Code99it/4F5LCD/displaypreviews/preview91D4.png

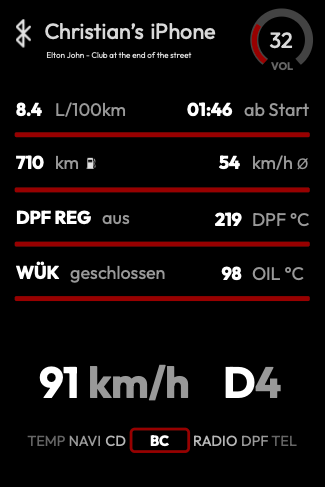
displaypreviews/preview91D4.png
