Code99it/4F5LCD/displaypreviews/preview.png

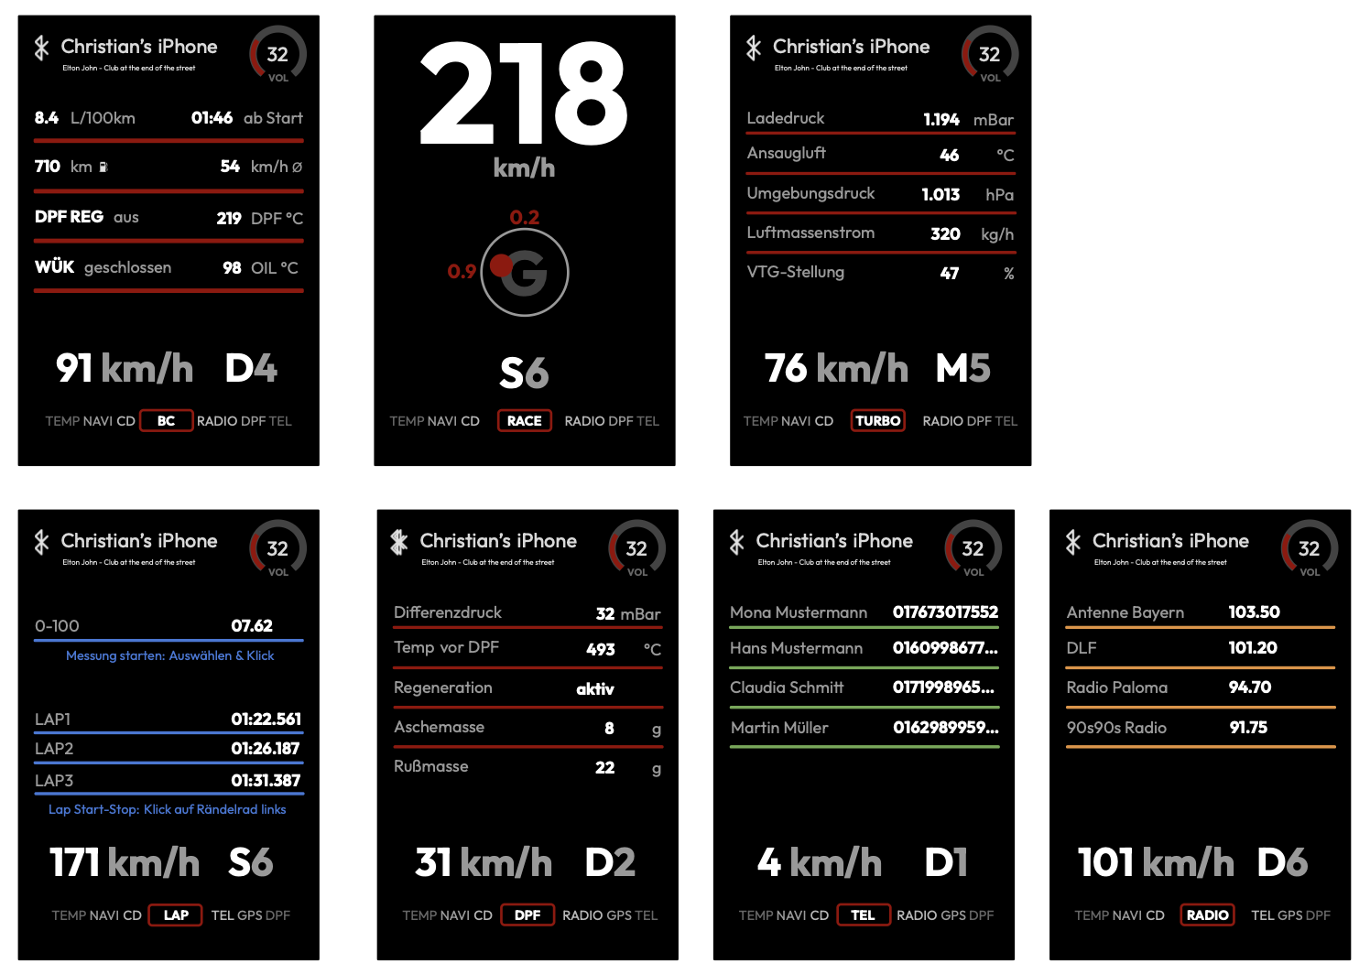
displaypreviews/preview.png
