Code99it/4F5LCD/ESP32-project/fonts/how-to-cut-a-letter.png

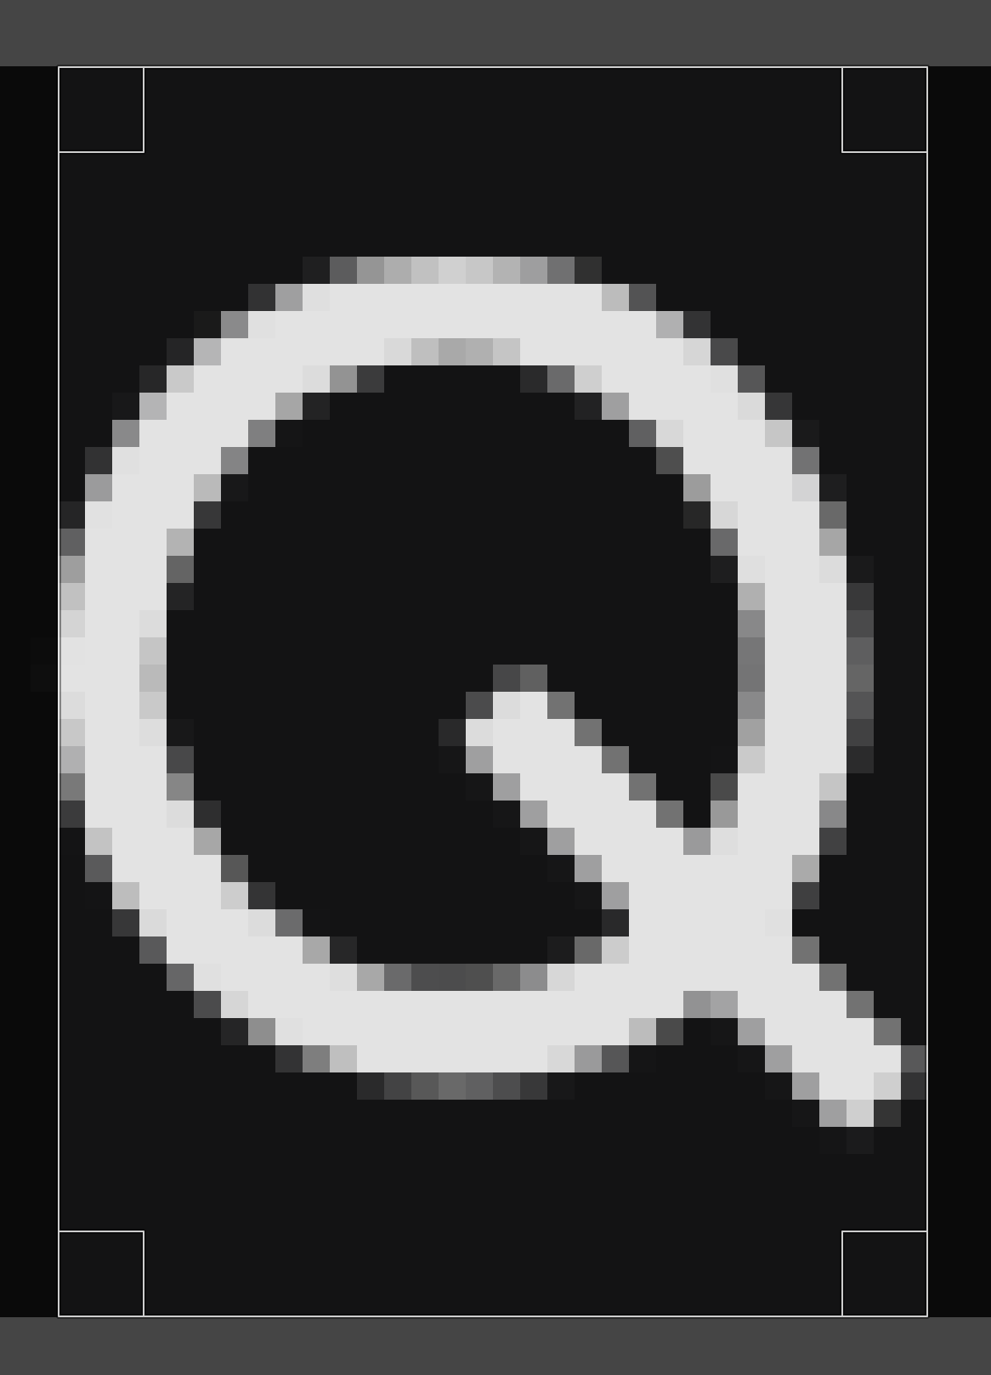
ESP32-project/fonts/how-to-cut-a-letter.png
