Code99it/4F5LCD/Solution 1 - 3D printed mounting frame for the LCD/PXL_20250601_192038704.jpg

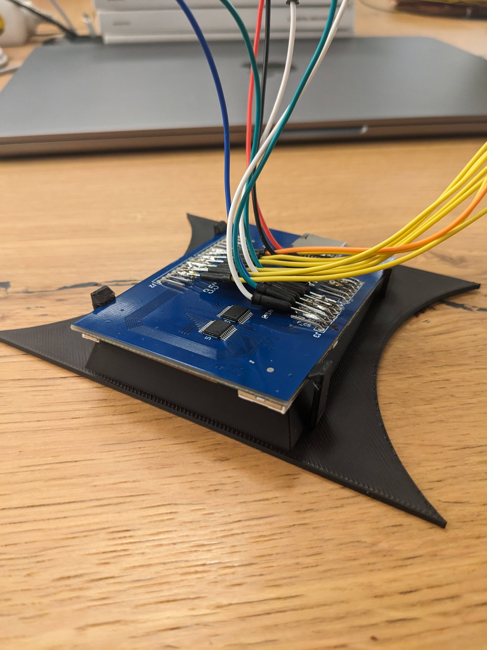
Solution 1 - 3D printed mounting frame for the LCD/PXL_20250601_192038704.jpg
