Code99it/4F5LCD/Solution 2 - Disassembling the speedometer and fitting a 3.5 inch display/PXL_20250607_091444971.jpg

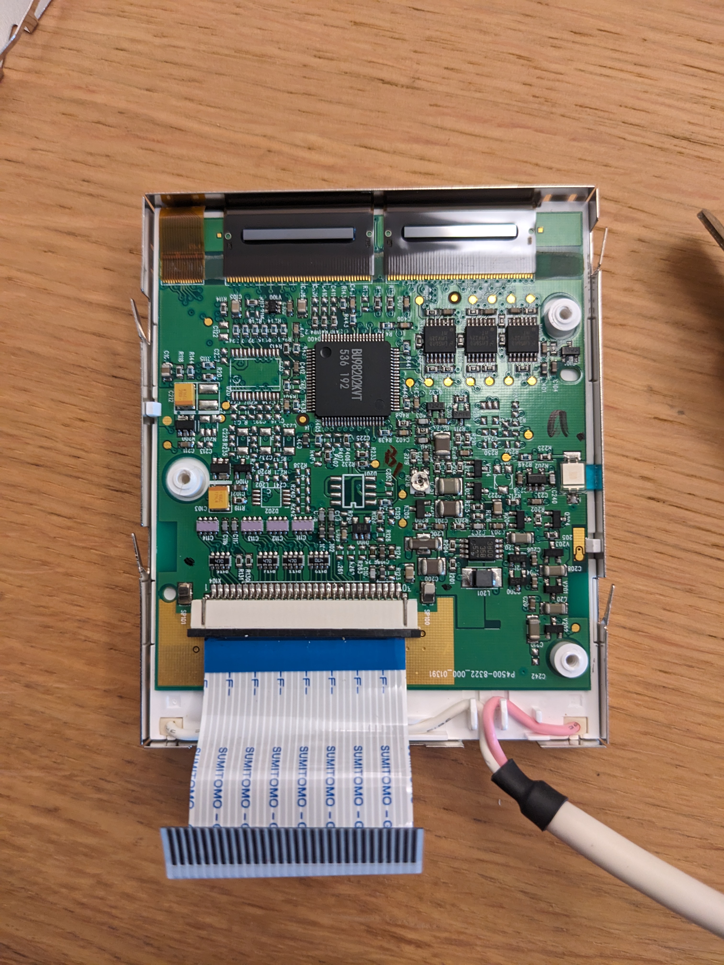
Solution 2 - Disassembling the speedometer and fitting a 3.5 inch display/PXL_20250607_091444971.jpg
