Code99it/4F5LCD/PCB printed circuit board/KiCad/100powersupply.kicad_sch

## KiCad design PCB printed circuit board/KiCad/100powersupply.kicad_sch (2025-06-01)

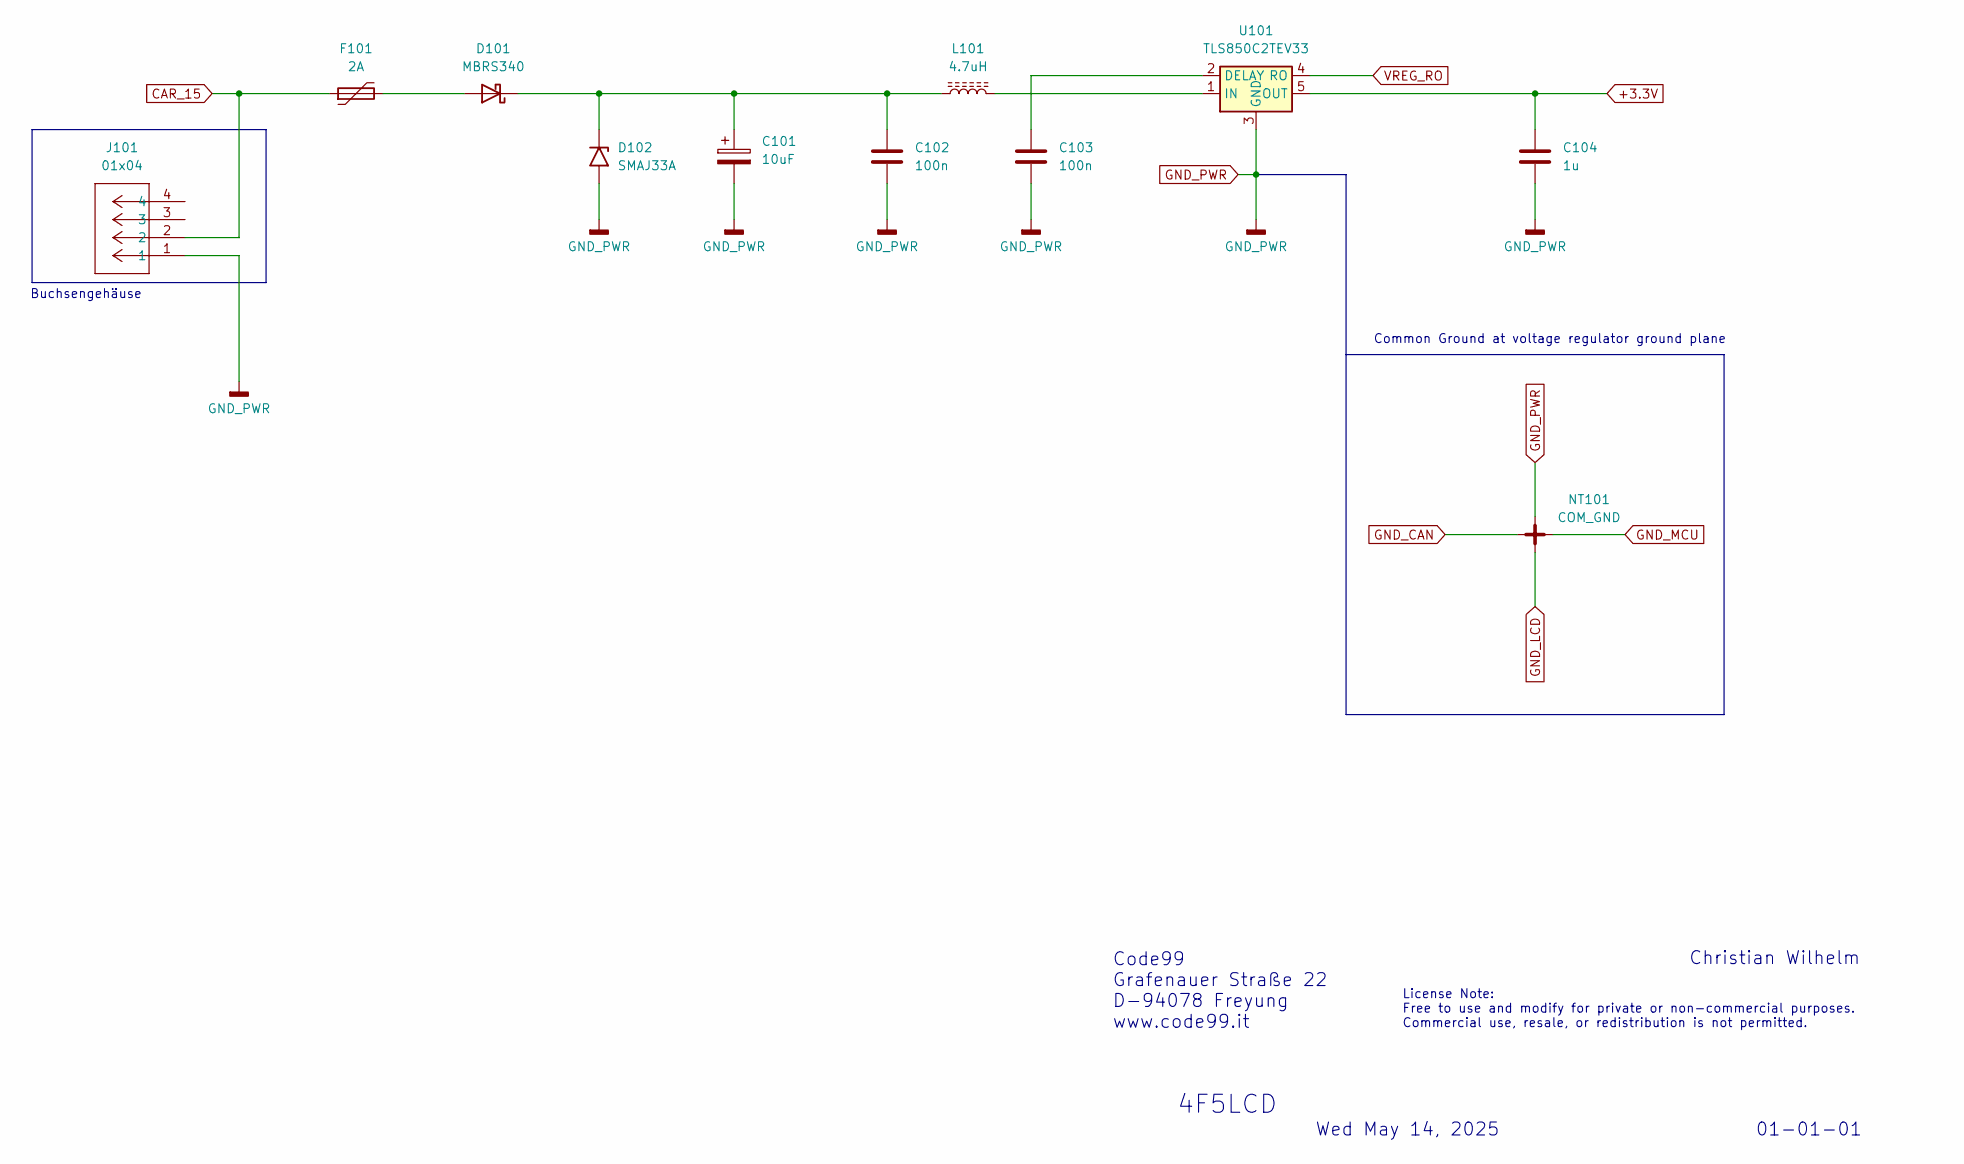
[picture p49: schematic 100powersupply.kicad_sch]

Parts:
C101: 10uF; CP_Elec_5x5.9; Farnell 2346378
C102, C103: 100n; C_1206_3216Metric_Pad1.33x1.80mm_HandSolder; Farnell 2495443
C104: 1u; C_1206_3216Metric_Pad1.33x1.80mm_HandSolder; Farnell 2357339
D101: MBRS340; D_SMC; Farnell 2824888
D102: SMAJ33A; D_SMA; Farnell 4065376
F101: 2A; Fuse_Bourns_MF-SM_7.98x5.44mm; Farnell 3605928
J101: 01x04; TE_MATE-N-LOK_1-770968-x_2x02_P4.14mm_Horizontal; Farnell 3394275
L101: 4.7uH; L_Radial_D7.5mm_P5.00mm_Fastron_07P
NT101: COM_GND
U101: TLS850C2TEV33; TO-252-4; Farnell 3680235

Connections:
+3.3V: C104.1, U101.5 (OUT)
CAR_15: F101.1, J101.2
GND_CAN: NT101.1
GND_LCD: NT101.4
GND_MCU: NT101.2
GND_PWR: C101.2, C102.2, C103.2, C104.2, D102.2 (A2), J101.1, NT101.3, U101.3 (GND)
unnamed: C101.1, C102.1, D101.1 (K), D102.1 (A1), L101.1
unnamed: C103.1, U101.2 (DELAY)
unnamed: D101.2 (A), F101.2
unnamed: L101.2, U101.1 (IN)
VREG_RO: U101.4 (RO)

Notes on the sheet:
Wed May 14, 2025
Code99 Grafenauer Straße 22 D-94078 Freyung www.code99.it
License Note: Free to use and modify for private or non-commercial purposes. Commercial use, resale, or redistribution is not permitted.
4F5LCD
01-01-01
Buchsengehäuse
Common Ground at voltage regulator ground plane
Christian Wilhelm
