Code99it/4F5LCD/PCB printed circuit board/KiCad/200mcuesp32.kicad_sch

## KiCad design PCB printed circuit board/KiCad/200mcuesp32.kicad_sch (2025-06-01)

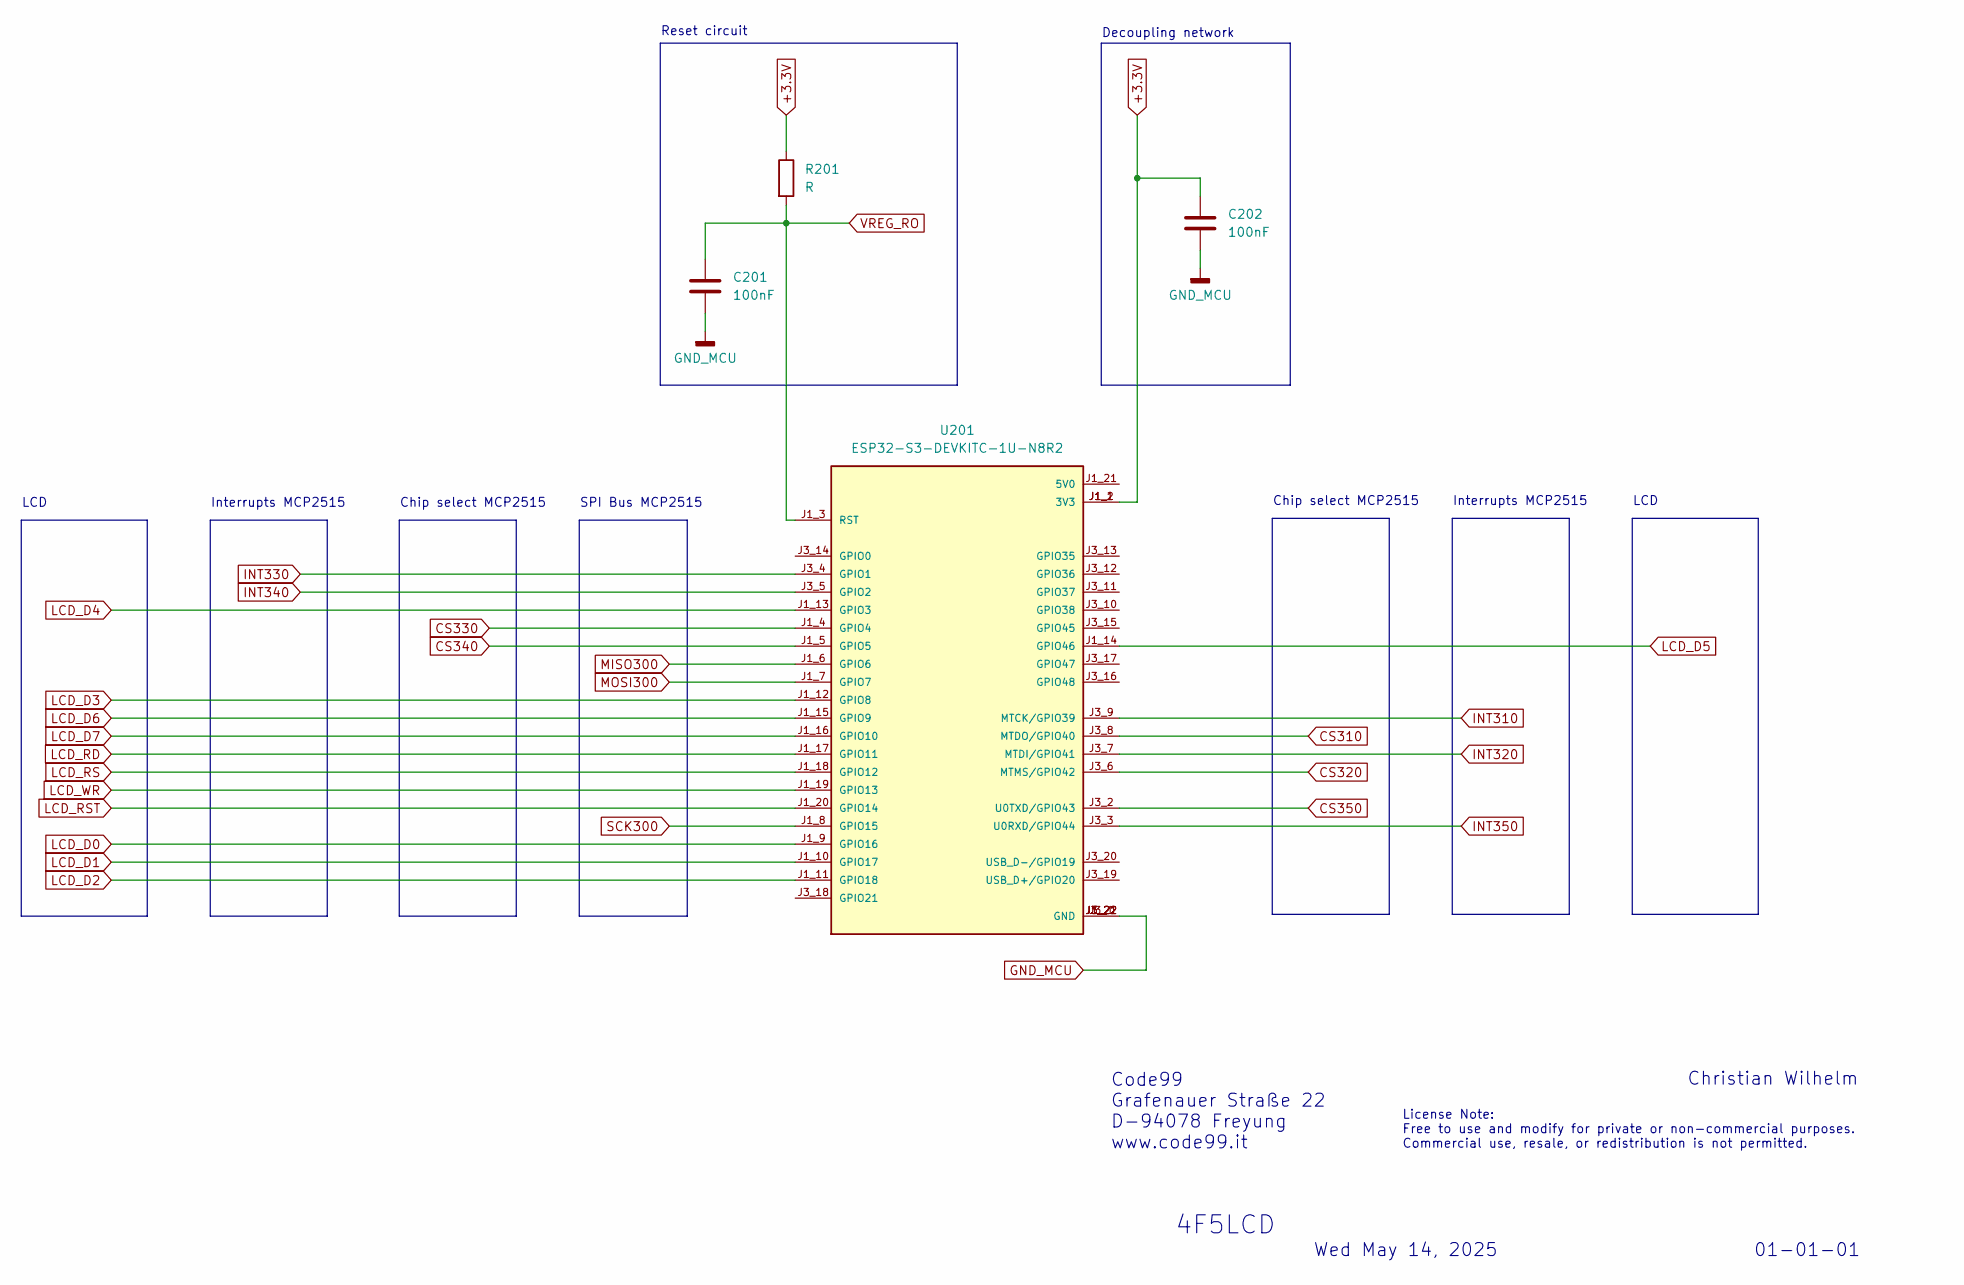
[picture p50: schematic 200mcuesp32.kicad_sch]

Parts:
C201: 100nF; Farnell 2495443
C202: 100nF; C_1206_3216Metric_Pad1.33x1.80mm_HandSolder; Farnell 2495443
R201: R; Farnell 1469856
U201: ESP32-S3-DEVKITC-1U-N8R2; XCVR_ESP32-S3-DEVKITC-1U-N8R2; PARTREV 5.3

Connections:
+3.3V: C202.1, R201.1, U201.J1_1 (3V3), U201.J1_2 (3V3)
CS310: U201.J3_8 (MTDO/GPIO40)
CS320: U201.J3_6 (MTMS/GPIO42)
CS330: U201.J1_4 (GPIO4)
CS340: U201.J1_5 (GPIO5)
CS350: U201.J3_2 (U0TXD/GPIO43)
GND_MCU: C201.2, C202.2, U201.J1_22 (GND), U201.J3_1 (GND), U201.J3_21 (GND), U201.J3_22 (GND)
INT310: U201.J3_9 (MTCK/GPIO39)
INT320: U201.J3_7 (MTDI/GPIO41)
INT330: U201.J3_4 (GPIO1)
INT340: U201.J3_5 (GPIO2)
INT350: U201.J3_3 (U0RXD/GPIO44)
LCD_D0: U201.J1_9 (GPIO16)
LCD_D1: U201.J1_10 (GPIO17)
LCD_D2: U201.J1_11 (GPIO18)
LCD_D3: U201.J1_12 (GPIO8)
LCD_D4: U201.J1_13 (GPIO3)
LCD_D5: U201.J1_14 (GPIO46)
LCD_D6: U201.J1_15 (GPIO9)
LCD_D7: U201.J1_16 (GPIO10)
LCD_RD: U201.J1_17 (GPIO11)
LCD_RS: U201.J1_18 (GPIO12)
LCD_RST: U201.J1_20 (GPIO14)
LCD_WR: U201.J1_19 (GPIO13)
MISO300: U201.J1_6 (GPIO6)
MOSI300: U201.J1_7 (GPIO7)
SCK300: U201.J1_8 (GPIO15)
VREG_RO: C201.1, R201.2, U201.J1_3 (RST)

Notes on the sheet:
License Note: Free to use and modify for private or non-commercial purposes. Commercial use, resale, or redistribution is not permitted.
LCD
01-01-01
Reset circuit
Chip select MCP2515
Interrupts MCP2515
Code99 Grafenauer Straße 22 D-94078 Freyung www.code99.it
Decoupling network
4F5LCD
SPI Bus MCP2515
Christian Wilhelm
Wed May 14, 2025
