Code99it/4F5LCD/PCB printed circuit board/KiCad/310connector.kicad_sch

## KiCad design PCB printed circuit board/KiCad/310connector.kicad_sch (2025-06-01)

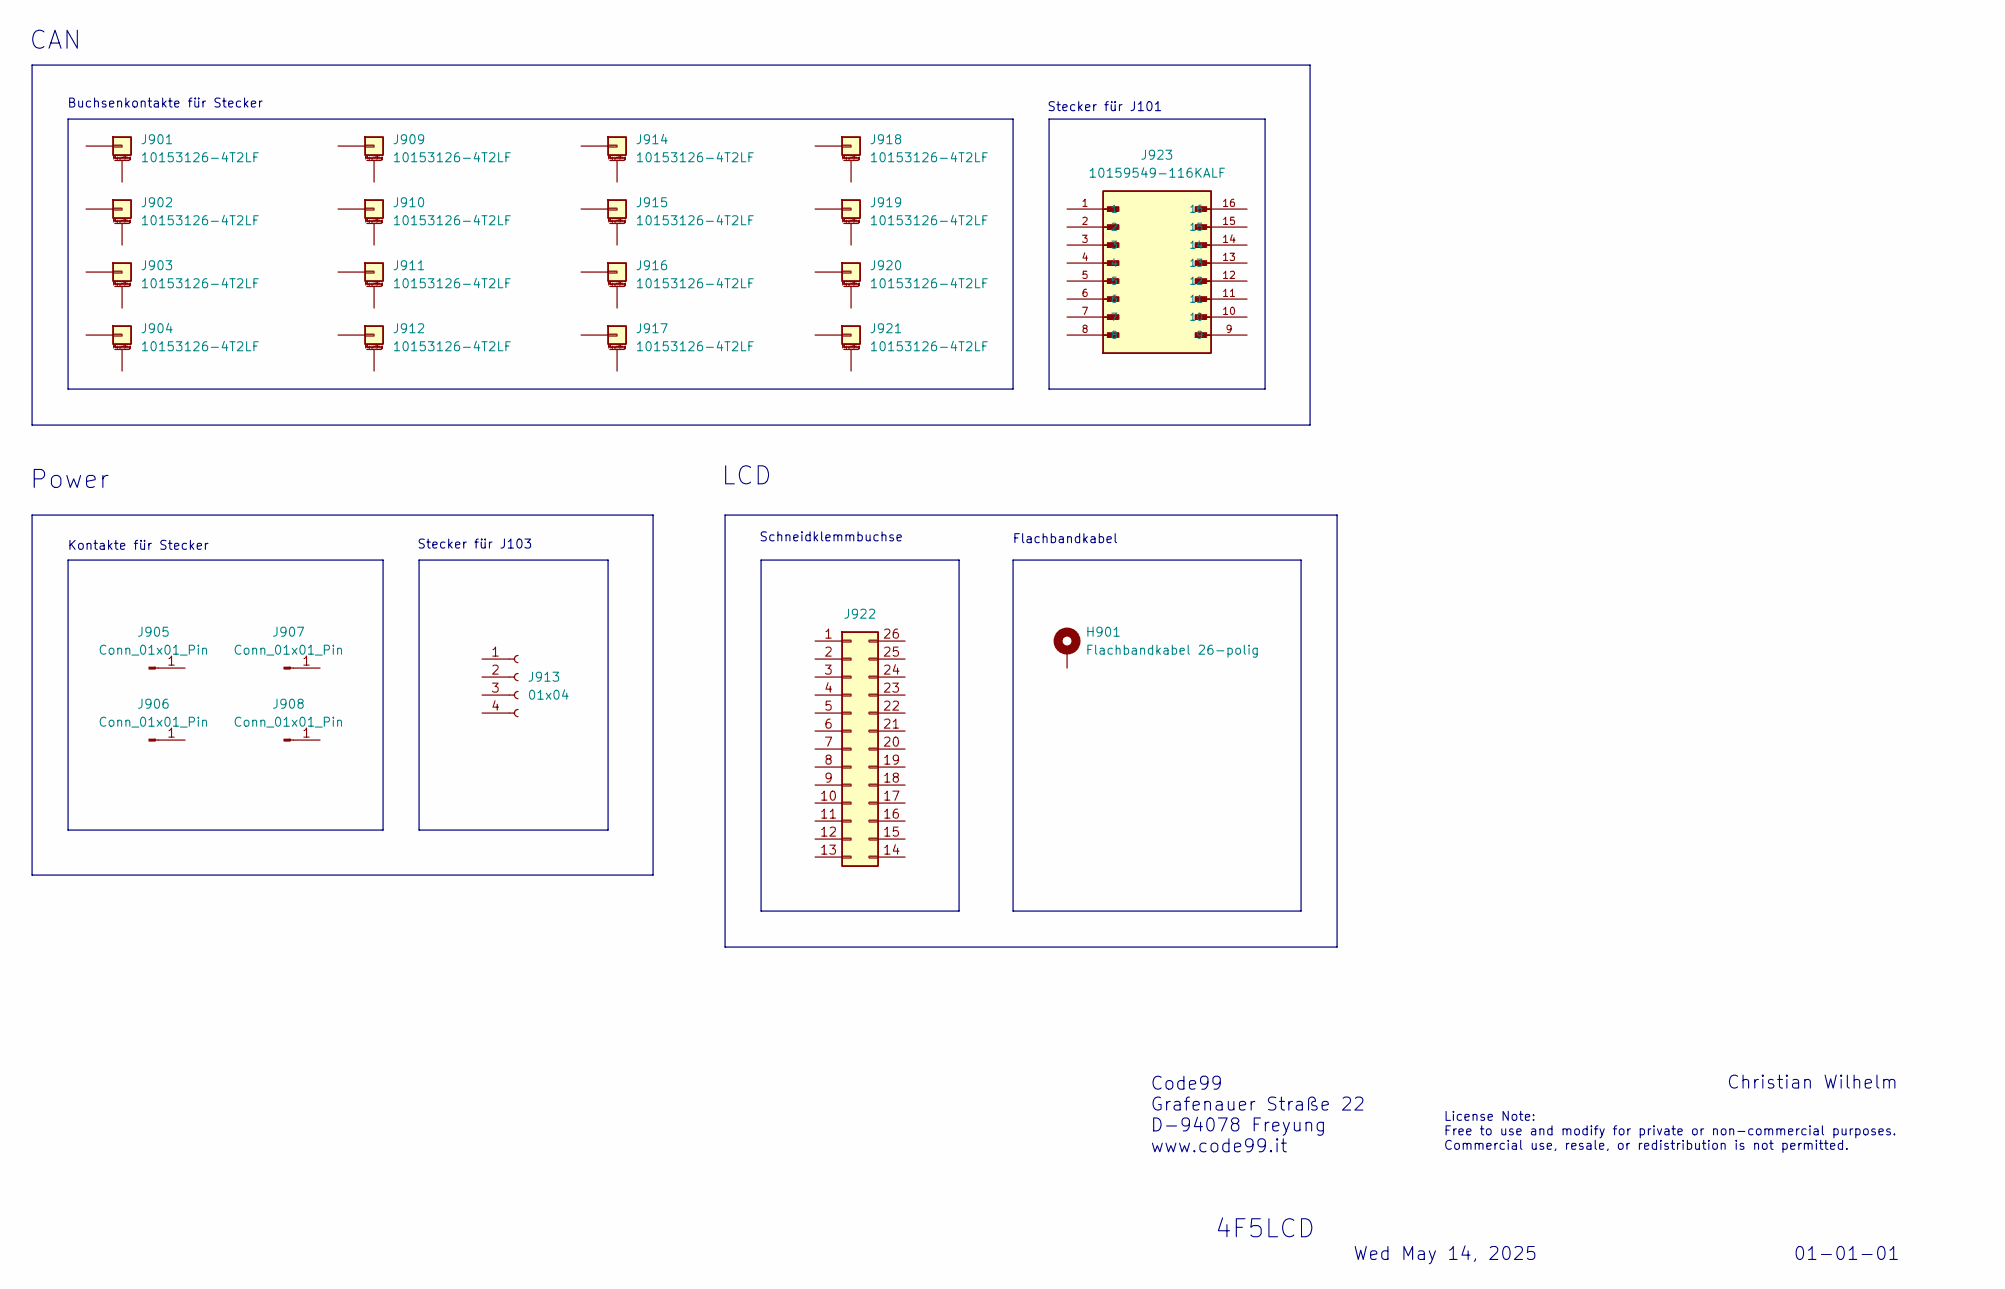
[picture p51: schematic 310connector.kicad_sch]

Parts:
H901: Flachbandkabel 26-polig; Farnell 2628366
J901, J902, J903, J904, J909, J910, J911, J912, J914, J915, J916, J917, J918, J919, J920, J921: 10153126-4T2LF; Farnell 3765472
J905, J906, J907, J908: Conn_01x01_Pin; Farnell 2530597
J913: 01x04; PhoenixContact_MC_1,5_2-G-3.81_1x02_P3.81mm_Horizontal; Farnell 3394278
J922: Conn_02x16_Top_Bottom; IDC-Header_2x13-1MP_P2.54mm_Latch_Horizontal; Farnell 2843502
J923: 10159549-116KALF; PARTREV G; Farnell 3765470

Notes on the sheet:
CAN
Christian Wilhelm
Power
Wed May 14, 2025
Kontakte für Stecker
Flachbandkabel
Buchsenkontakte für Stecker
License Note: Free to use and modify for private or non-commercial purposes. Commercial use, resale, or redistribution is not permitted.
Stecker für J103
Code99 Grafenauer Straße 22 D-94078 Freyung www.code99.it
Schneidklemmbuchse
LCD
Stecker für J101
4F5LCD
01-01-01
