Code99it/4F5LCD/PCB printed circuit board/KiCad/400lcd.kicad_sch

## KiCad design PCB printed circuit board/KiCad/400lcd.kicad_sch (2025-06-01)

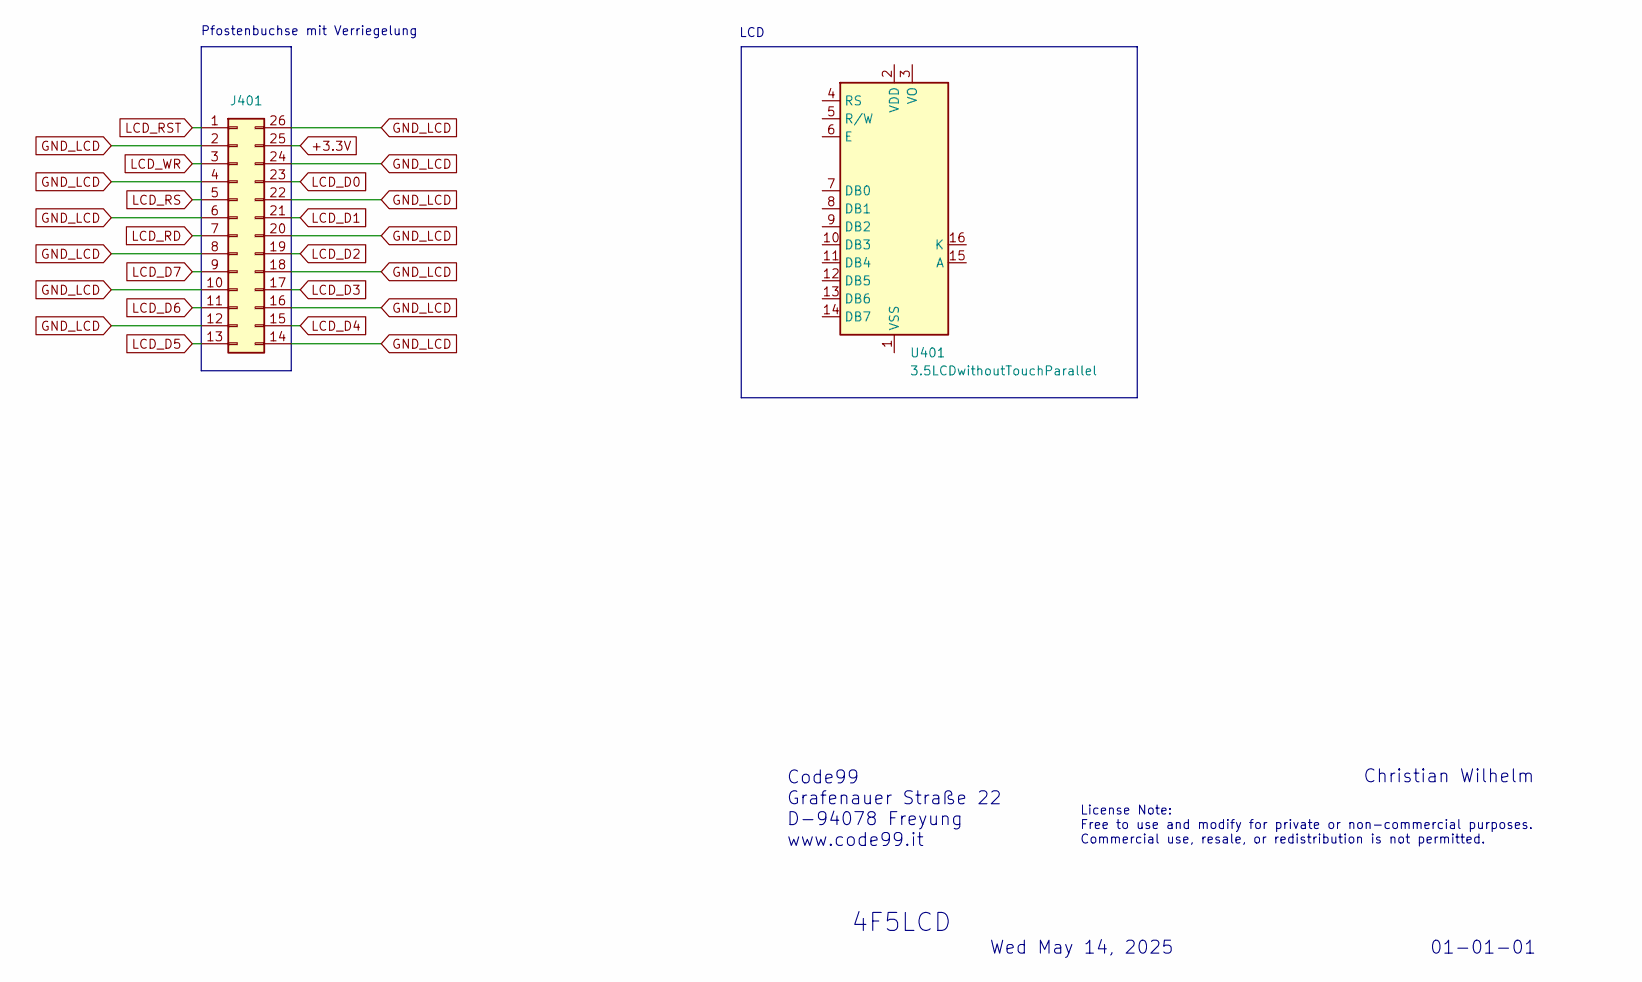
[picture p52: schematic 400lcd.kicad_sch]

Parts:
J401: Conn_02x16_Top_Bottom; IDC-Header_2x13-1MP_P2.54mm_Latch_Horizontal; Farnell 2843590
U401: 3.5LCDwithoutTouchParallel; NHD-0420H1Z

Connections:
+3.3V: J401.25
GND_LCD: J401.2, J401.4, J401.6, J401.8, J401.10, J401.12, J401.14, J401.16, J401.18, J401.20, J401.22, J401.24, J401.26
LCD_D0: J401.23
LCD_D1: J401.21
LCD_D2: J401.19
LCD_D3: J401.17
LCD_D4: J401.15
LCD_D5: J401.13
LCD_D6: J401.11
LCD_D7: J401.9
LCD_RD: J401.7
LCD_RS: J401.5
LCD_RST: J401.1
LCD_WR: J401.3

Notes on the sheet:
License Note: Free to use and modify for private or non-commercial purposes. Commercial use, resale, or redistribution is not permitted.
01-01-01
Code99 Grafenauer Straße 22 D-94078 Freyung www.code99.it
LCD
4F5LCD
Christian Wilhelm
Wed May 14, 2025
Pfostenbuchse mit Verriegelung
