Code99it/4F5LCD/PCB printed circuit board/KiCad/CANcomfort.kicad_sch

## KiCad design PCB printed circuit board/KiCad/CANcomfort.kicad_sch (2025-06-01)

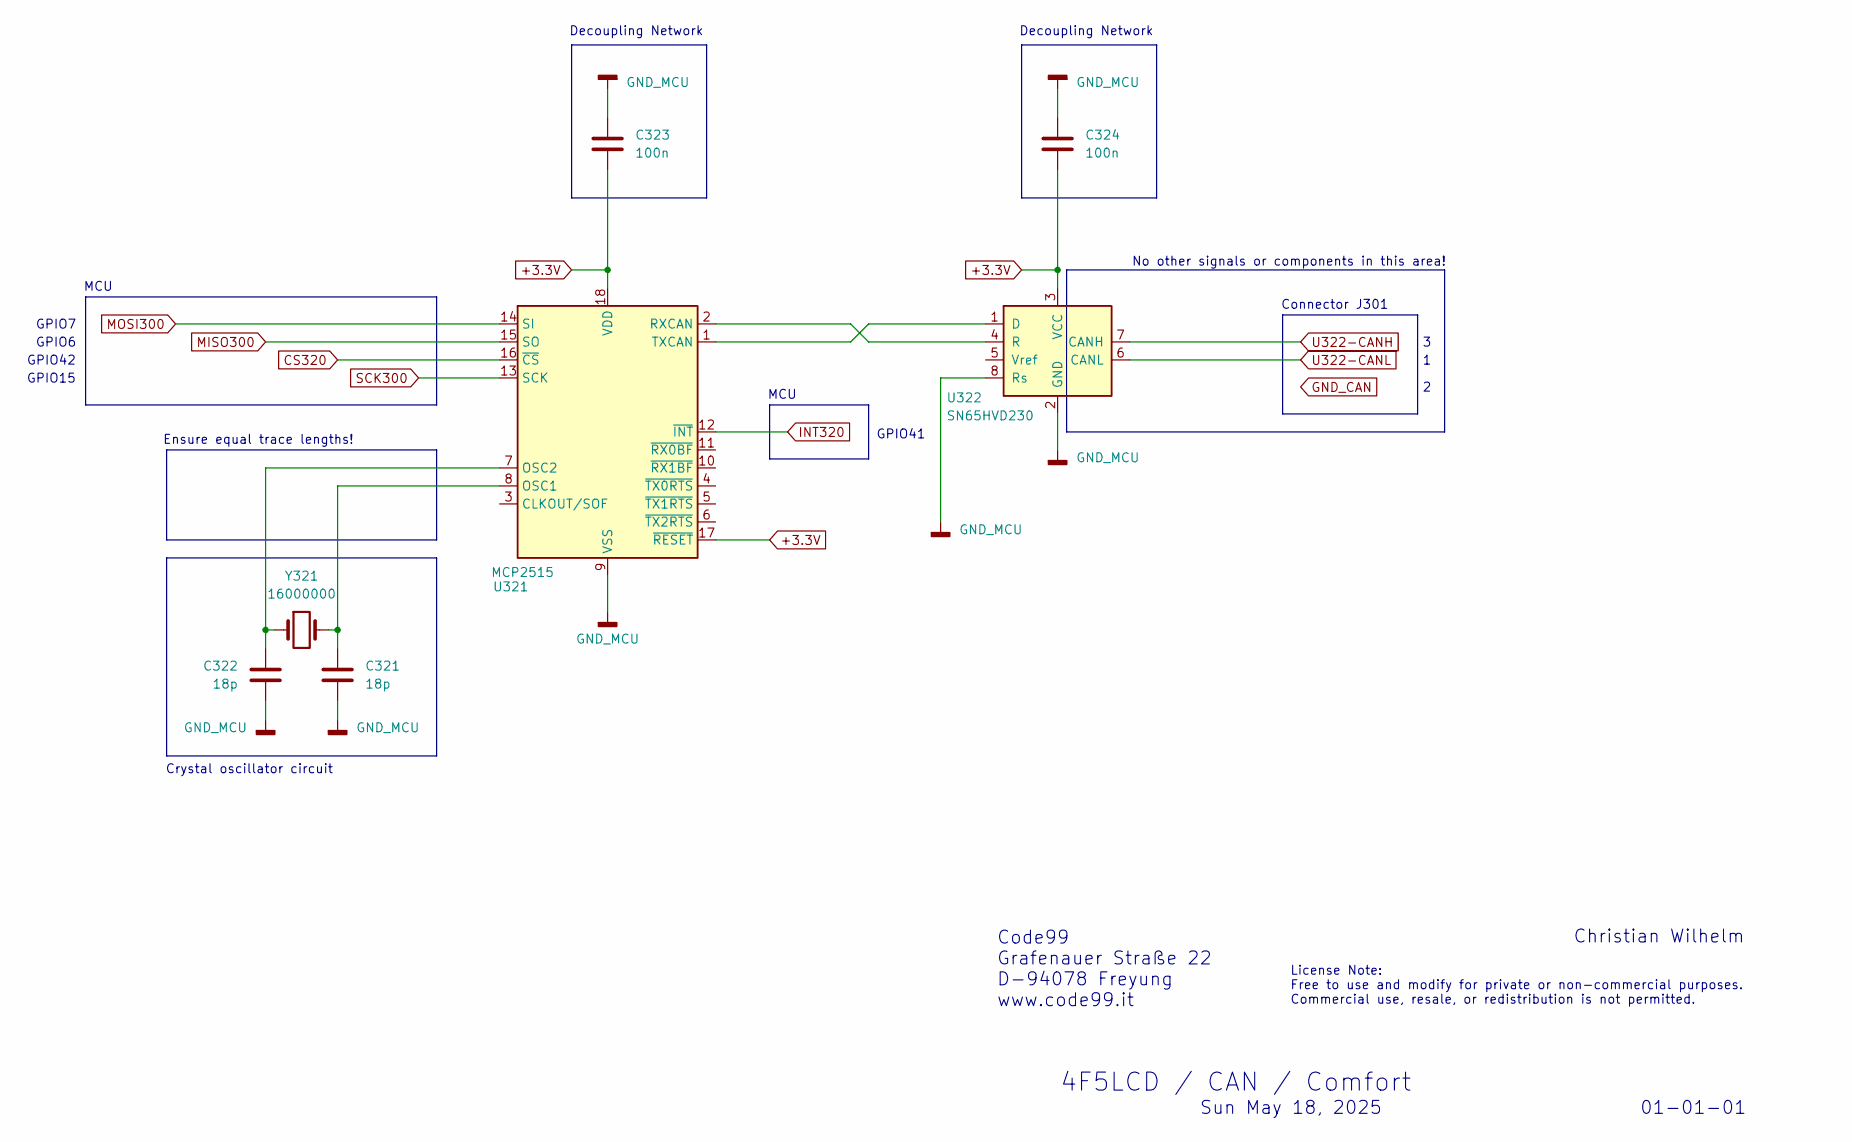
[picture p53: schematic CANcomfort.kicad_sch]

Parts:
C321, C322: 18p; C_0603_1608Metric; Farnell 2905608
C323, C324: 100n; C_1206_3216Metric; Farnell 2495443
U321: MCP2515; SOIC-18W_7.5x11.6mm_P1.27mm; Farnell 1292239
U322: SN65HVD230; SOIC-8_3.9x4.9mm_P1.27mm; Farnell 3124671
Y321: 16000000; Crystal_SMD_Abracon_ABM3-2Pin_5.0x3.2mm; Farnell 2832079

Connections:
+3.3V: C323.2, C324.1, U321.17 (~RESET), U321.18 (VDD), U322.3 (VCC)
CS320: U321.16 (~CS)
GND_MCU: C321.2, C322.1, C323.1, C324.2, U321.9 (VSS), U322.2 (GND), U322.8 (Rs)
INT320: U321.12 (~INT)
MISO300: U321.15 (SO)
MOSI300: U321.14 (SI)
unnamed: C321.1, U321.8 (OSC1), Y321.2
unnamed: C322.2, U321.7 (OSC2), Y321.1
unnamed: U321.1 (TXCAN), U322.1 (D)
unnamed: U321.2 (RXCAN), U322.4 (R)
SCK300: U321.13 (SCK)
U322-CANH: U322.7 (CANH)
U322-CANL: U322.6 (CANL)

Notes on the sheet:
MCU
Ensure equal trace lengths!
GPIO42
License Note: Free to use and modify for private or non-commercial purposes. Commercial use, resale, or redistribution is not permitted.
GPIO15
Code99 Grafenauer Straße 22 D-94078 Freyung www.code99.it
GPIO7
Sun May 18, 2025
Christian Wilhelm
Connector J301
GPIO6
Decoupling Network
01-01-01
4F5LCD / CAN / Comfort
No other signals or components in this area!
GPIO41
Crystal oscillator circuit
