Code99it/4F5LCD/PCB printed circuit board/KiCad/CANin.kicad_sch

## KiCad design PCB printed circuit board/KiCad/CANin.kicad_sch (2025-06-01)

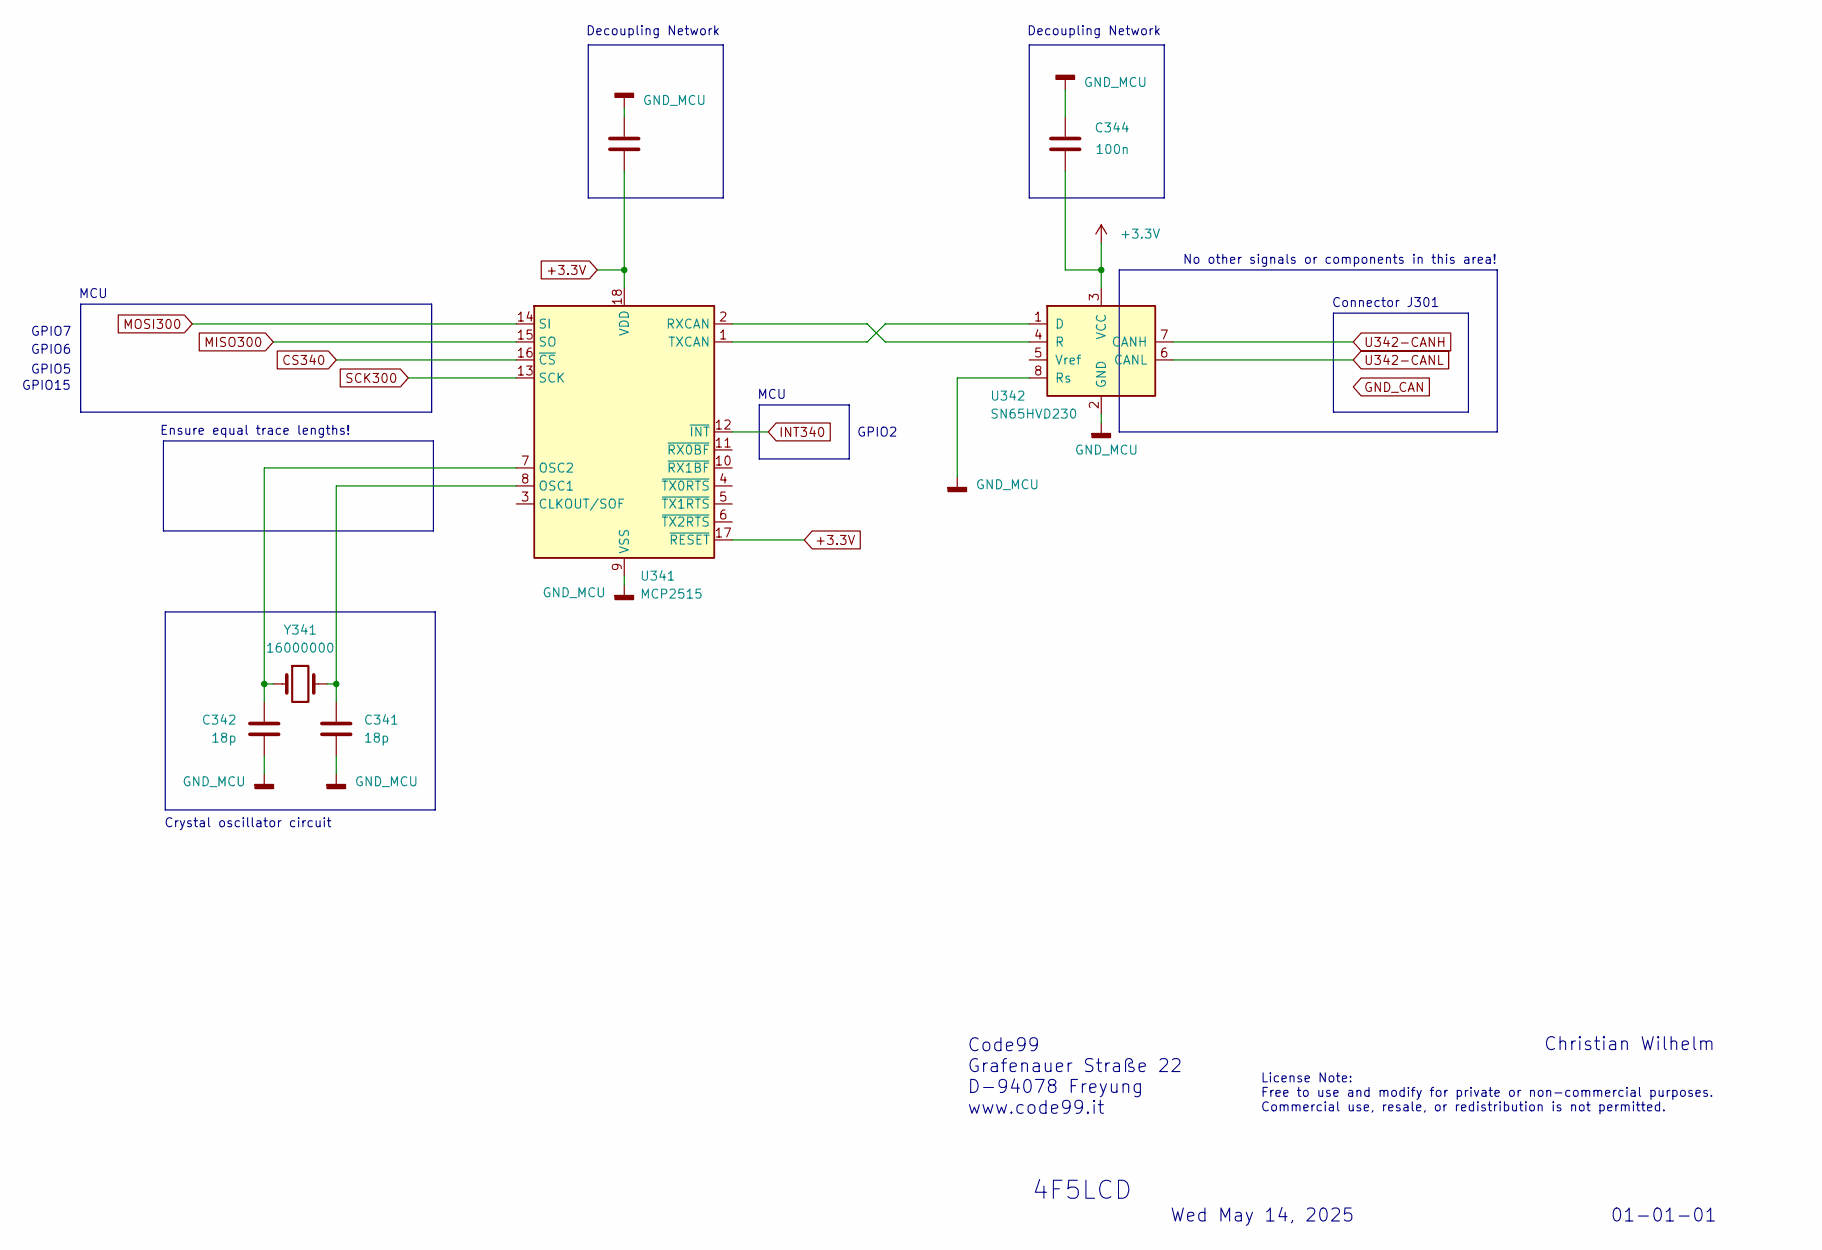
[picture p54: schematic CANin.kicad_sch]

Parts:
C341, C342: 18p; C_0603_1608Metric; Farnell 2905608
C343, C344: 100n; C_1206_3216Metric; Farnell 2495443
U341: MCP2515; SOIC-18W_7.5x11.6mm_P1.27mm; Farnell 1292239
U342: SN65HVD230; SOIC-8_3.9x4.9mm_P1.27mm; Farnell 3124671
Y341: 16000000; Crystal_SMD_Abracon_ABM3-2Pin_5.0x3.2mm; Farnell 2832079

Connections:
+3.3V: C343.1, C344.1, U341.17 (~RESET), U341.18 (VDD), U342.3 (VCC)
CS340: U341.16 (~CS)
GND_MCU: C341.2, C342.1, C343.2, C344.2, U341.9 (VSS), U342.2 (GND), U342.8 (Rs)
INT340: U341.12 (~INT)
MISO300: U341.15 (SO)
MOSI300: U341.14 (SI)
unnamed: C341.1, U341.8 (OSC1), Y341.2
unnamed: C342.2, U341.7 (OSC2), Y341.1
unnamed: U341.1 (TXCAN), U342.1 (D)
unnamed: U341.2 (RXCAN), U342.4 (R)
SCK300: U341.13 (SCK)
U342-CANH: U342.7 (CANH)
U342-CANL: U342.6 (CANL)

Notes on the sheet:
4F5LCD
GPIO6
Connector J301
MCU
Ensure equal trace lengths!
Decoupling Network
GPIO5
License Note: Free to use and modify for private or non-commercial purposes. Commercial use, resale, or redistribution is not permitted.
01-01-01
GPIO2
GPIO15
Christian Wilhelm
GPIO7
Wed May 14, 2025
Crystal oscillator circuit
Code99 Grafenauer Straße 22 D-94078 Freyung www.code99.it
No other signals or components in this area!
