Code99it/4F5LCD/PCB printed circuit board/KiCad/CANinfo.kicad_sch

## KiCad design PCB printed circuit board/KiCad/CANinfo.kicad_sch (2025-06-01)

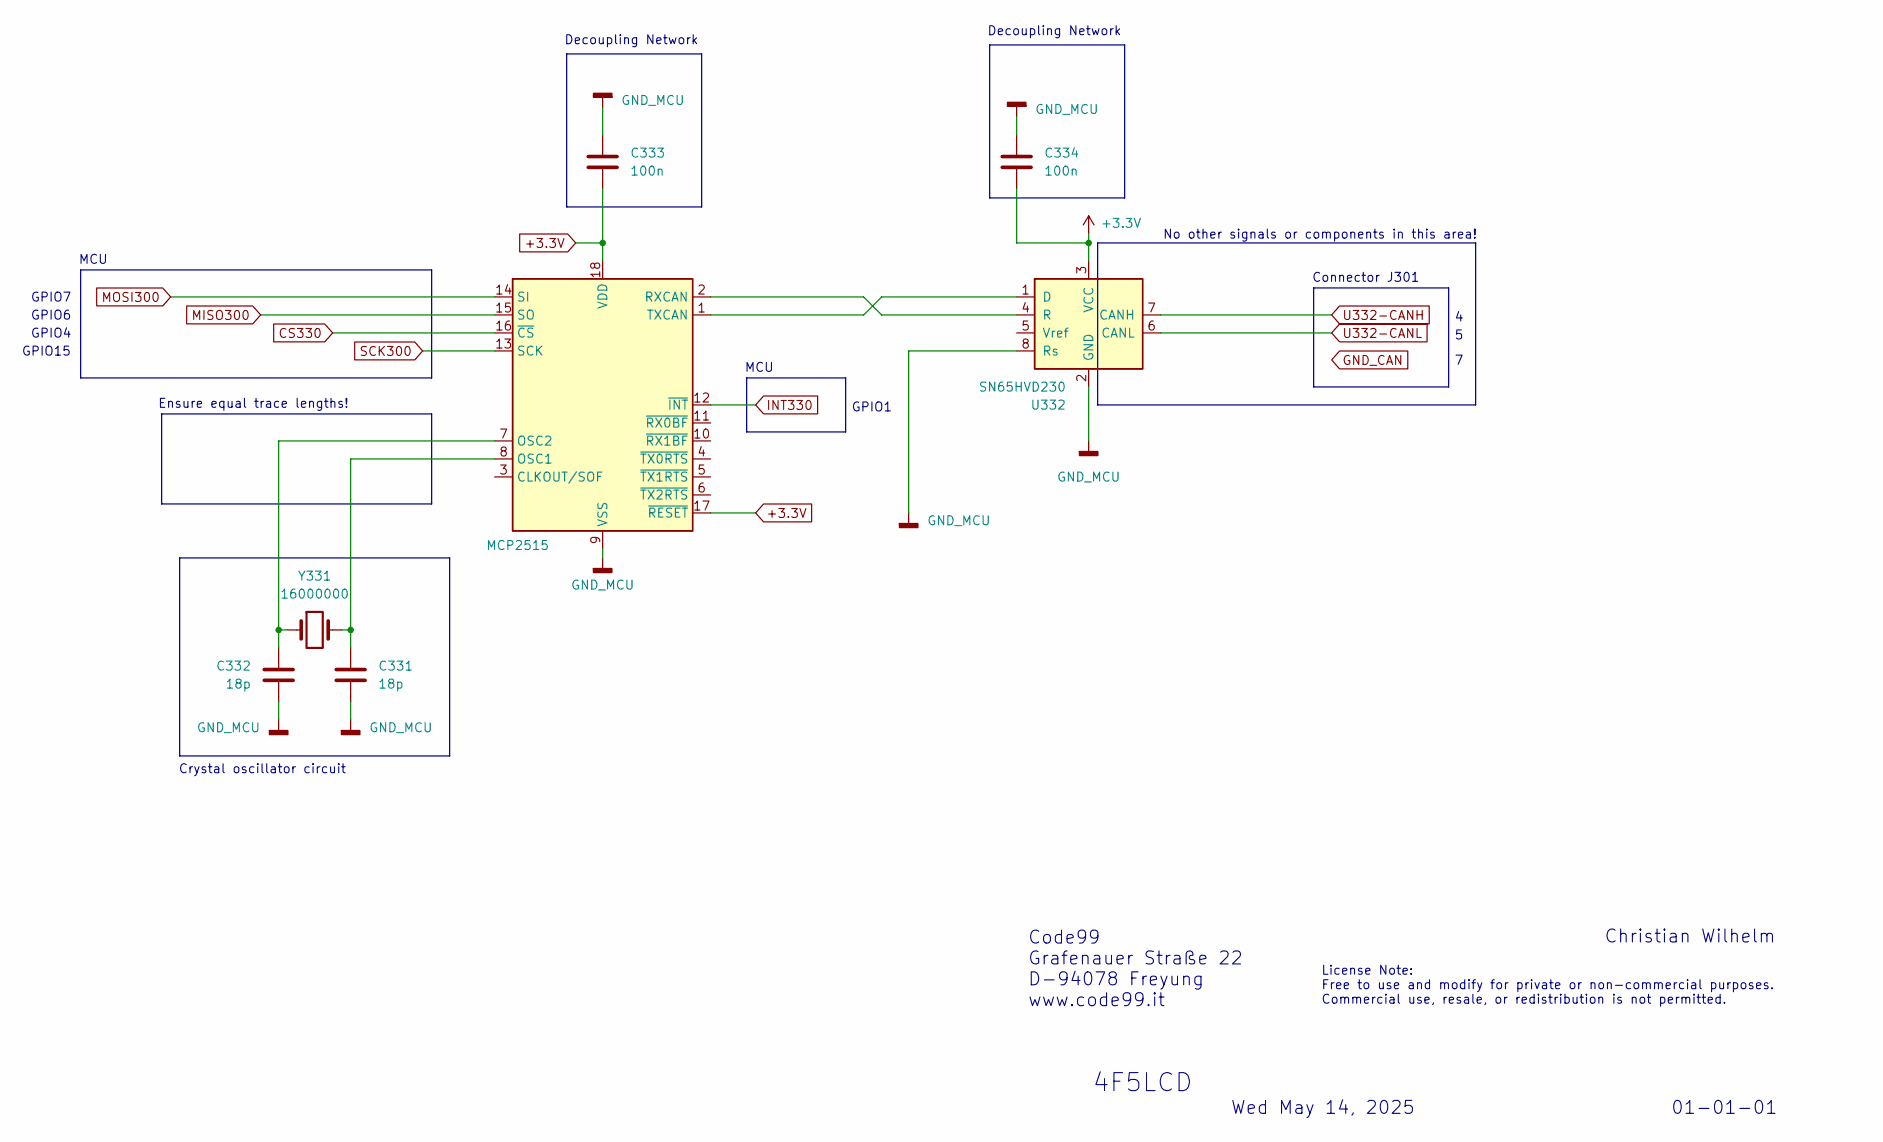
[picture p55: schematic CANinfo.kicad_sch]

Parts:
C331, C332: 18p; C_0603_1608Metric; Farnell 2905608
C333, C334: 100n; C_1206_3216Metric; Farnell 2495443
U331: MCP2515; SOIC-18W_7.5x11.6mm_P1.27mm; Farnell 1292239
U332: SN65HVD230; SOIC-8_3.9x4.9mm_P1.27mm; Farnell 3124671
Y331: 16000000; Crystal_SMD_Abracon_ABM3-2Pin_5.0x3.2mm; Farnell 2832079

Connections:
+3.3V: C333.1, C334.1, U331.17 (~RESET), U331.18 (VDD), U332.3 (VCC)
CS330: U331.16 (~CS)
GND_MCU: C331.2, C332.1, C333.2, C334.2, U331.9 (VSS), U332.2 (GND), U332.8 (Rs)
INT330: U331.12 (~INT)
MISO300: U331.15 (SO)
MOSI300: U331.14 (SI)
unnamed: C331.1, U331.8 (OSC1), Y331.2
unnamed: C332.2, U331.7 (OSC2), Y331.1
unnamed: U331.1 (TXCAN), U332.1 (D)
unnamed: U331.2 (RXCAN), U332.4 (R)
SCK300: U331.13 (SCK)
U332-CANH: U332.7 (CANH)
U332-CANL: U332.6 (CANL)

Notes on the sheet:
Christian Wilhelm
MCU
Ensure equal trace lengths!
GPIO7
GPIO1
GPIO6
Crystal oscillator circuit
GPIO15
No other signals or components in this area!
Connector J301
Decoupling Network
01-01-01
Wed May 14, 2025
GPIO4
4F5LCD
Code99 Grafenauer Straße 22 D-94078 Freyung www.code99.it
License Note: Free to use and modify for private or non-commercial purposes. Commercial use, resale, or redistribution is not permitted.
