Code99it/4F5LCD/PCB printed circuit board/KiCad/CANout.kicad_sch

## KiCad design PCB printed circuit board/KiCad/CANout.kicad_sch (2025-06-01)

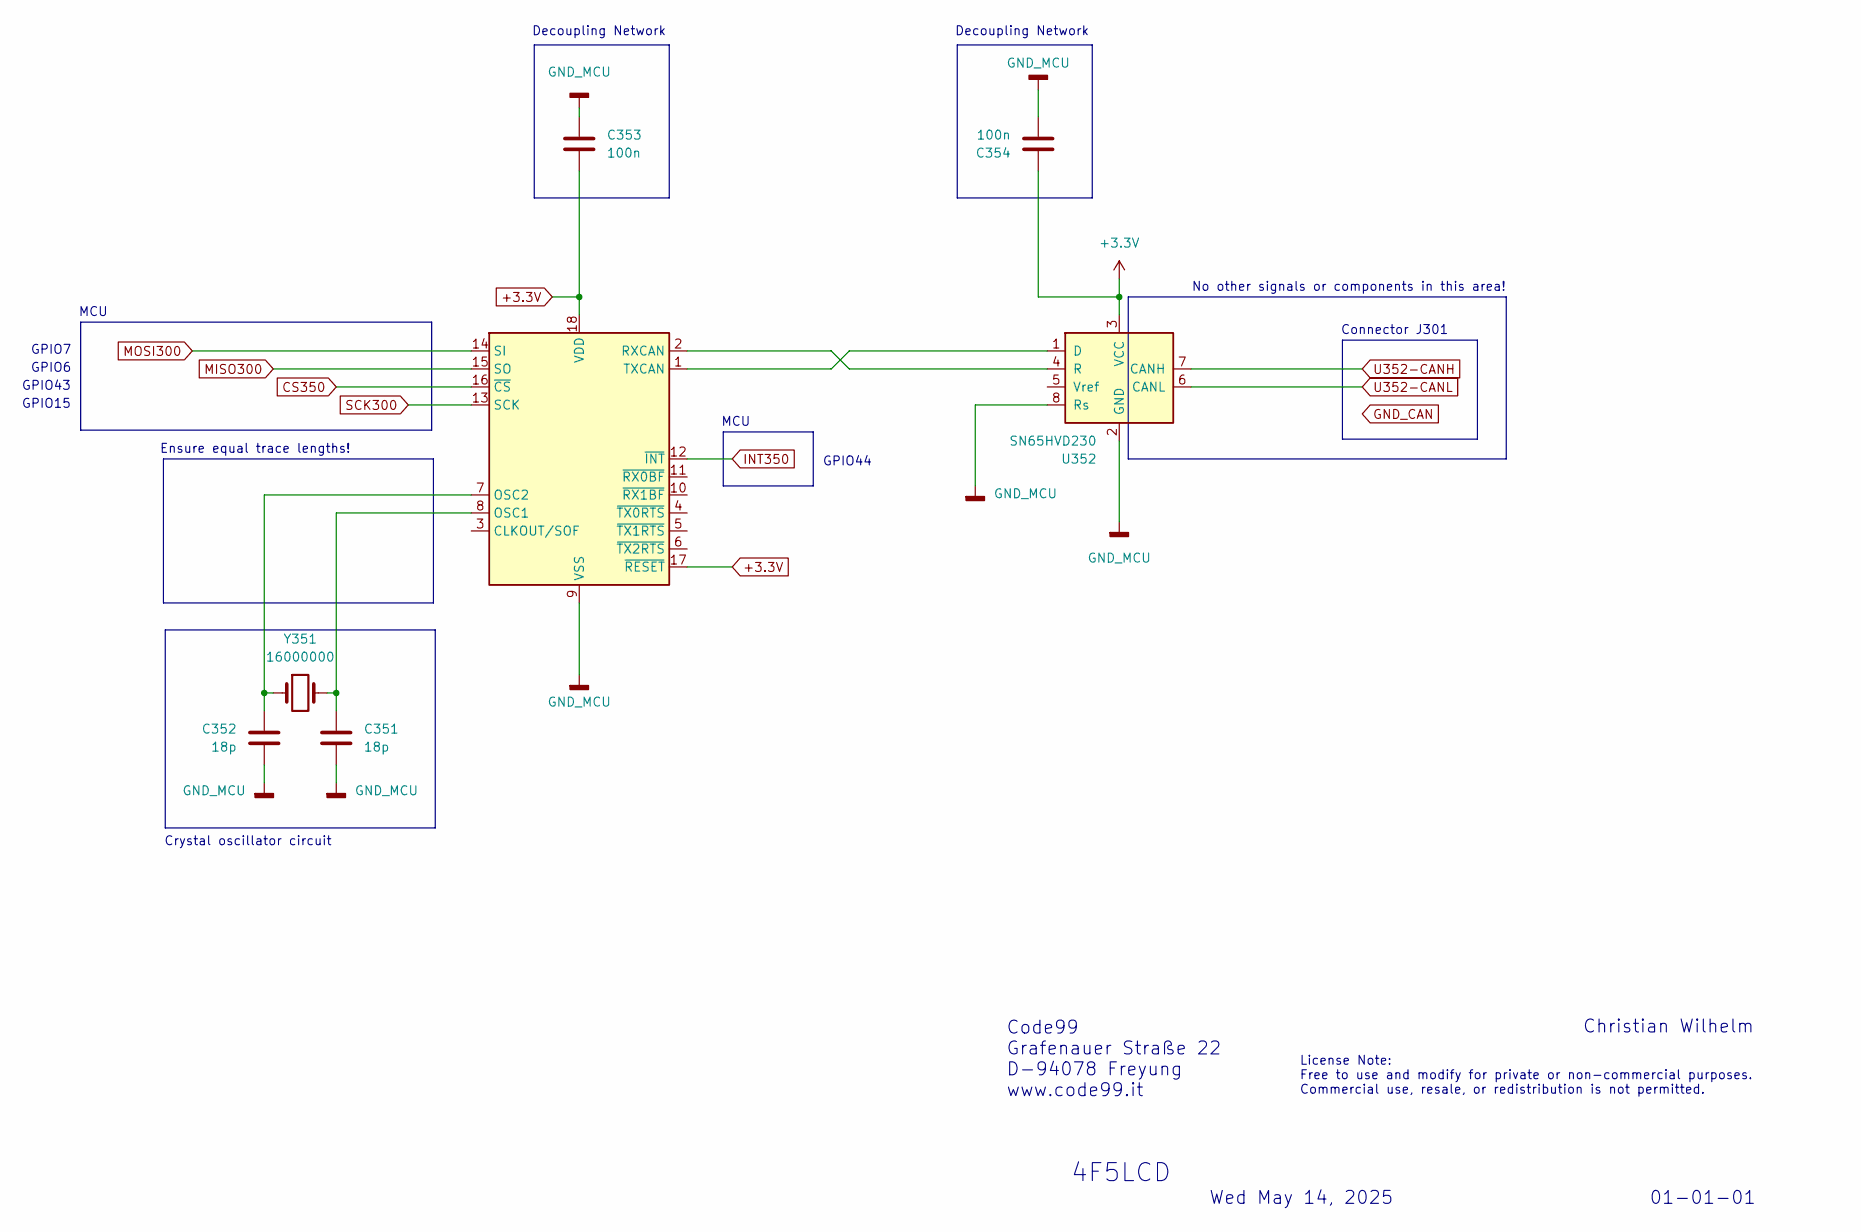
[picture p56: schematic CANout.kicad_sch]

Parts:
C351, C352: 18p; C_0603_1608Metric; Farnell 2905608
C353, C354: 100n; C_1206_3216Metric; Farnell 2495443
U351: MCP2515; SOIC-18W_7.5x11.6mm_P1.27mm; Farnell 1292239
U352: SN65HVD230; SOIC-8_3.9x4.9mm_P1.27mm; Farnell 3124671
Y351: 16000000; Crystal_SMD_Abracon_ABM3-2Pin_5.0x3.2mm; Farnell 2832079

Connections:
+3.3V: C353.1, C354.1, U351.17 (~RESET), U351.18 (VDD), U352.3 (VCC)
CS350: U351.16 (~CS)
GND_MCU: C351.2, C352.1, C353.2, C354.2, U351.9 (VSS), U352.2 (GND), U352.8 (Rs)
INT350: U351.12 (~INT)
MISO300: U351.15 (SO)
MOSI300: U351.14 (SI)
unnamed: C351.1, U351.8 (OSC1), Y351.2
unnamed: C352.2, U351.7 (OSC2), Y351.1
unnamed: U351.1 (TXCAN), U352.1 (D)
unnamed: U351.2 (RXCAN), U352.4 (R)
SCK300: U351.13 (SCK)
U352-CANH: U352.7 (CANH)
U352-CANL: U352.6 (CANL)

Notes on the sheet:
Christian Wilhelm
GPIO44
4F5LCD
MCU
Connector J301
GPIO15
No other signals or components in this area!
Decoupling Network
GPIO6
GPIO43
GPIO7
Crystal oscillator circuit
Code99 Grafenauer Straße 22 D-94078 Freyung www.code99.it
01-01-01
Ensure equal trace lengths!
License Note: Free to use and modify for private or non-commercial purposes. Commercial use, resale, or redistribution is not permitted.
Wed May 14, 2025
