Code99it/4F5LCD/PCB printed circuit board/KiCad/CANpowertrain.kicad_sch

## KiCad design PCB printed circuit board/KiCad/CANpowertrain.kicad_sch (2025-06-01)

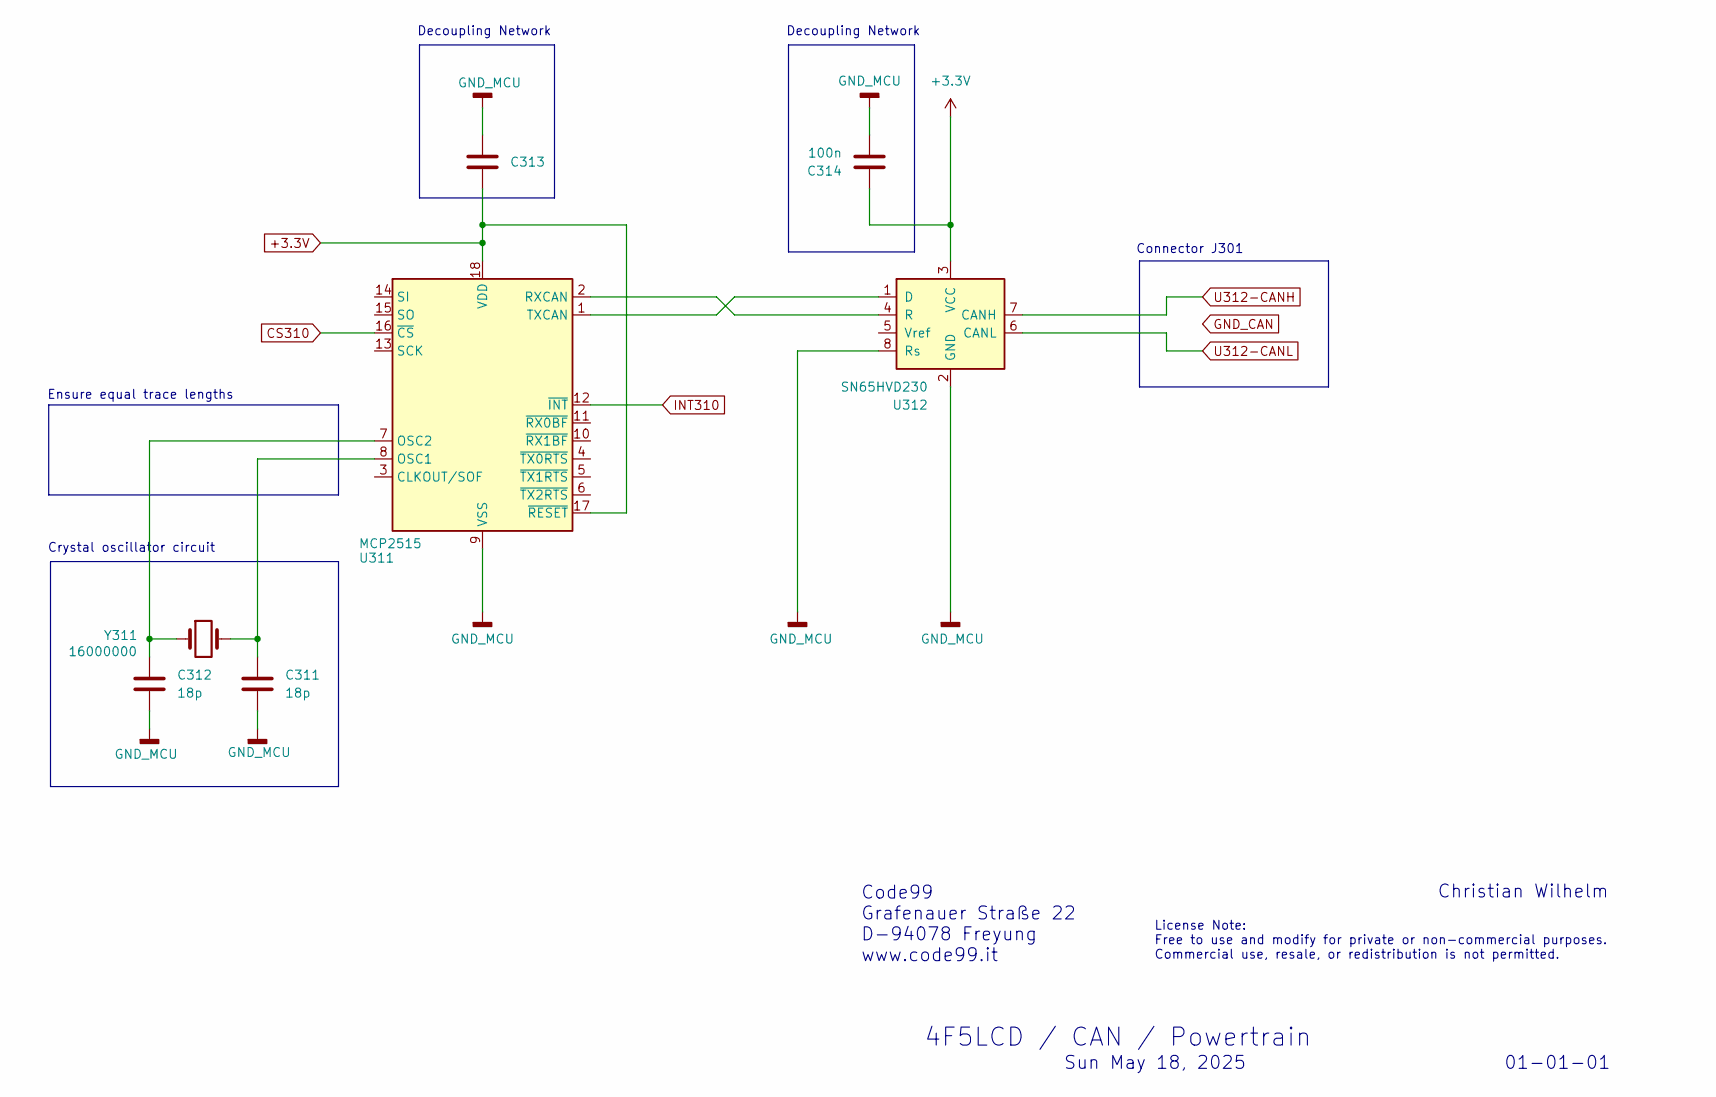
[picture p57: schematic CANpowertrain.kicad_sch]

Parts:
C311, C312: 18p; C_0603_1608Metric; Farnell 2905608
C313, C314: 100n; C_1206_3216Metric; Farnell 2495443
U311: MCP2515; SOIC-18W_7.5x11.6mm_P1.27mm; Farnell 1292239
U312: SN65HVD230; SOIC-8_3.9x4.9mm_P1.27mm; Farnell 3124671
Y311: 16000000; Crystal_SMD_Abracon_ABM3-2Pin_5.0x3.2mm; Farnell 2832079

Connections:
+3.3V: C313.1, C314.1, U311.17 (~RESET), U311.18 (VDD), U312.3 (VCC)
CS310: U311.16 (~CS)
GND_MCU: C311.2, C312.1, C313.2, C314.2, U311.9 (VSS), U312.2 (GND), U312.8 (Rs)
INT310: U311.12 (~INT)
unnamed: C311.1, U311.8 (OSC1), Y311.2
unnamed: C312.2, U311.7 (OSC2), Y311.1
unnamed: U311.1 (TXCAN), U312.1 (D)
unnamed: U311.2 (RXCAN), U312.4 (R)
U312-CANH: U312.7 (CANH)
U312-CANL: U312.6 (CANL)

Notes on the sheet:
Decoupling Network
01-01-01
Crystal oscillator circuit
License Note: Free to use and modify for private or non-commercial purposes. Commercial use, resale, or redistribution is not permitted.
Ensure equal trace lengths
4F5LCD / CAN / Powertrain
Sun May 18, 2025
Christian Wilhelm
Connector J301
Code99 Grafenauer Straße 22 D-94078 Freyung www.code99.it
