Code99it/4F5LCD/ESP32-project/main/Code99-API-LCD-ILI9486.h

#include <stdint.h>

#ifndef CODE99_API_LCD_ILI9486_H
#define CODE99_API_LCD_ILI9486_H

void lcd_draw_rect (uint16_t x1, uint16_t y1, uint16_t x2, uint16_t y2, uint16_t color);
void lcd_draw_test_pattern();

#endif
