Code99it/4F5LCD/ESP32-project/main/color.c

#include "color.h"

uint16_t color_888_to_565(uint32_t color) {
    uint8_t r = (color >> 16) & 0xFF;
    uint8_t g = (color >> 8) & 0xFF;
    uint8_t b = color & 0xFF;

    uint16_t r5 = (r * 31) / 255;
    uint16_t g6 = (g * 63) / 255;
    uint16_t b5 = (b * 31) / 255;

    return (r5 << 11) | (g6 << 5) | b5;
}
